dnschneid/espleak/example/ioboard.kicad_sch

## KiCad design example/ioboard.kicad_sch (2025-01-08)

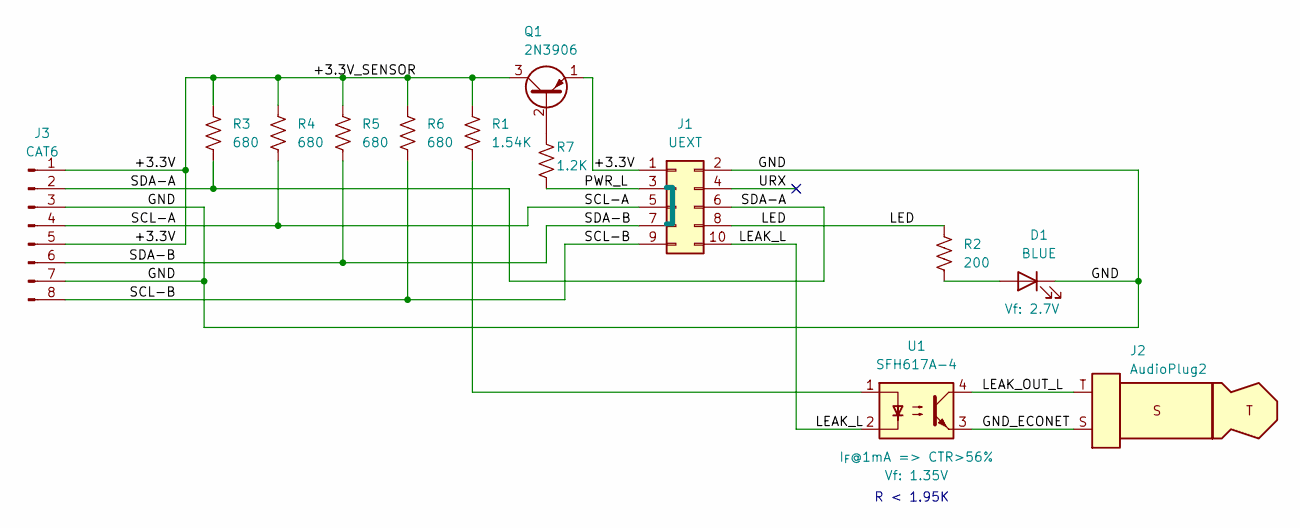
[picture p7: schematic ioboard.kicad_sch]

Parts:
D1: BLUE
J1: UEXT
J2: AudioPlug2
J3: CAT6
Q1: 2N3906; TO-92_Inline
R1: 1.54K
R2: 200
R3, R4, R5, R6: 680
R7: 1.2K
U1: SFH617A-4; DIP-4_W7.62mm

Connections:
+3.3V: J1.1, J3.1, J3.5, Q1.1 (E), Q1.3 (C), R1.1, R3.1, R4.1, R5.1, R6.1
GND: D1.1 (K), J1.2, J3.3, J3.7
GND_ECONET: J2.S, U1.3
LEAK_L: J1.10, U1.2
LEAK_OUT_L: J2.T, U1.4
LED: J1.8, R2.1
unnamed: D1.2 (A), R2.2
unnamed: Q1.2 (B), R7.1
unnamed: R1.2, U1.1
PWR_L: J1.3, R7.2
SCL-A: J1.5, J3.4, R4.2
SCL-B: J1.9, J3.8, R6.2
SDA-A: J1.6, J3.2, R3.2
SDA-B: J1.7, J3.6, R5.2
URX: J1.4

Notes on the sheet:
R < 1.95K
